eshazen/blinky-pov/AVR4/prog/prog_large.png

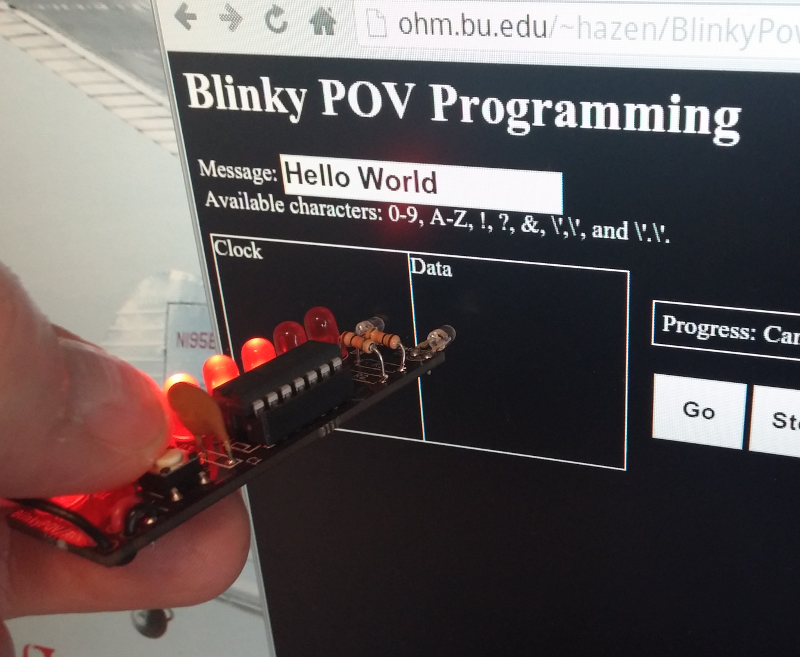
AVR4/prog/prog_large.png
