eshazen/blinky-pov/BlinkyColorPOV/pix/2015-11-30 16.28.32.jpg

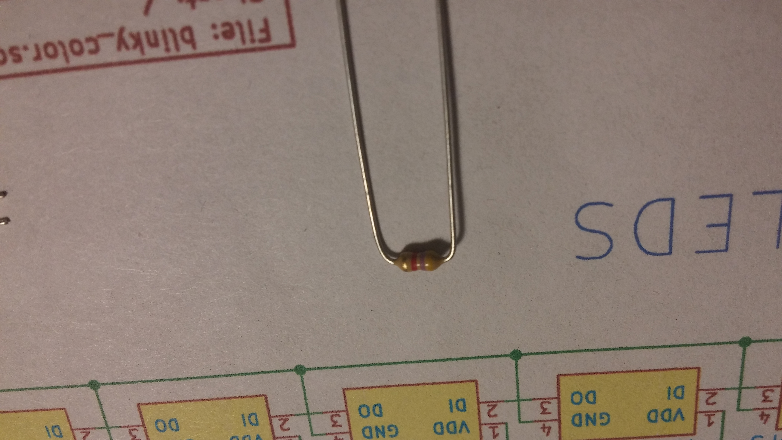
BlinkyColorPOV/pix/2015-11-30 16.28.32.jpg
