eshazen/blinky-pov/BlinkyColorPOV/pix/2015-11-30 16.30.00.jpg

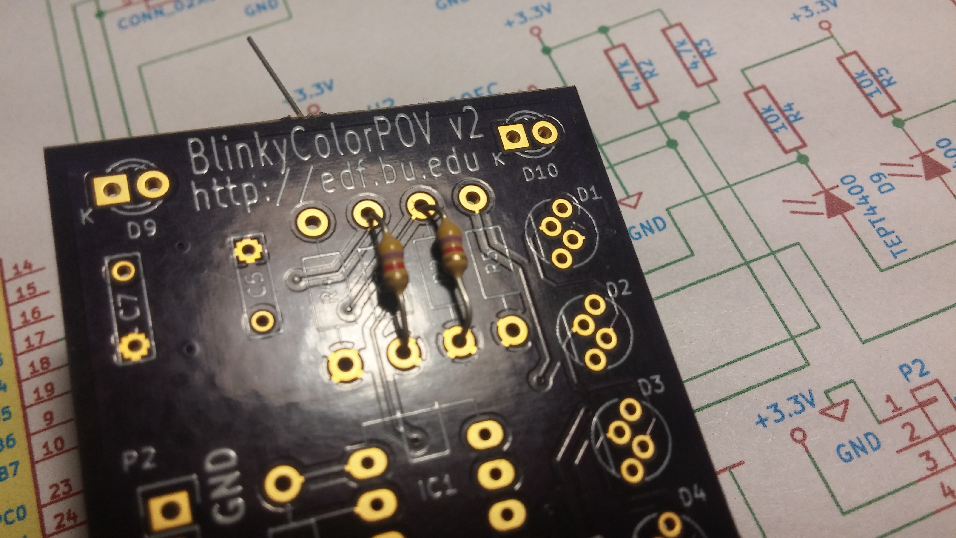
BlinkyColorPOV/pix/2015-11-30 16.30.00.jpg
