eshazen/blinky-pov/BlinkyColorPOV/pix/2015-11-30 16.31.33.jpg

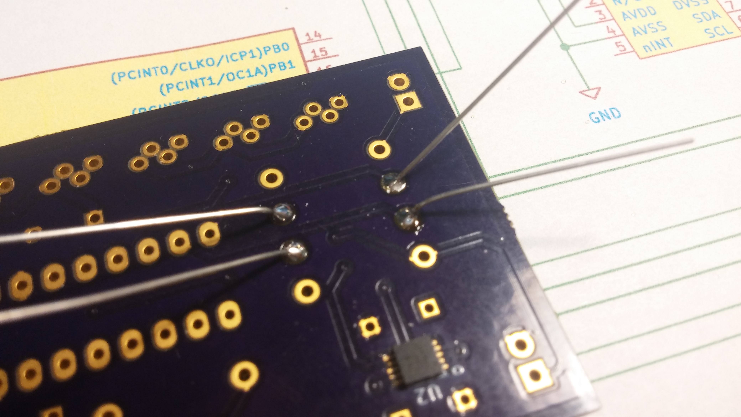
BlinkyColorPOV/pix/2015-11-30 16.31.33.jpg
