eshazen/blinky-pov/BlinkyColorPOV/pix/2015-11-30 16.32.19.jpg

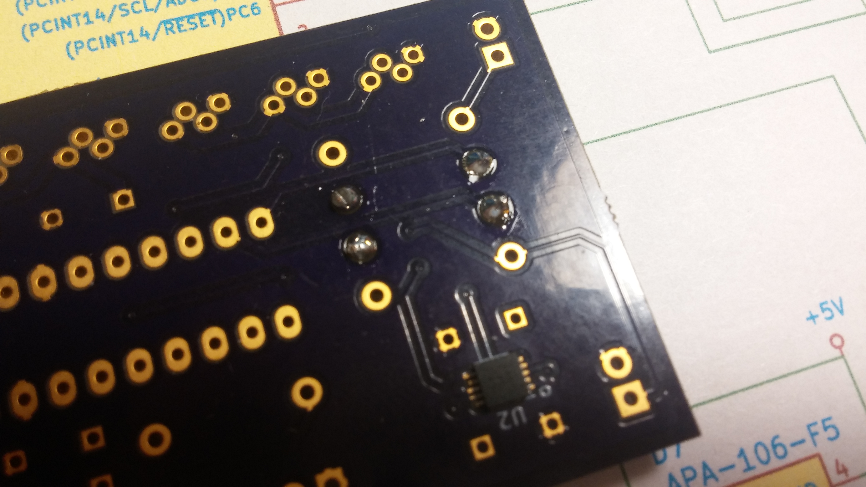
BlinkyColorPOV/pix/2015-11-30 16.32.19.jpg
