eshazen/blinky-pov/BlinkyColorPOV/pix/2015-11-30 16.37.39.jpg

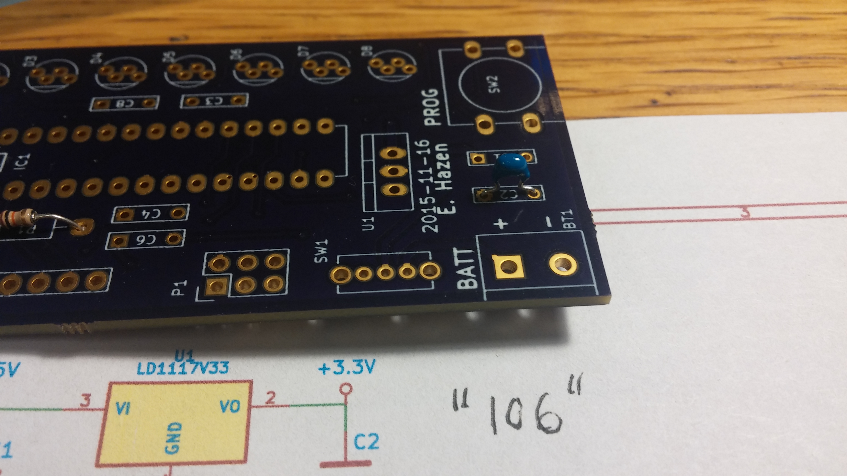
BlinkyColorPOV/pix/2015-11-30 16.37.39.jpg
