eshazen/blinky-pov/BlinkyColorPOV/pix/2015-11-30 16.41.47.jpg

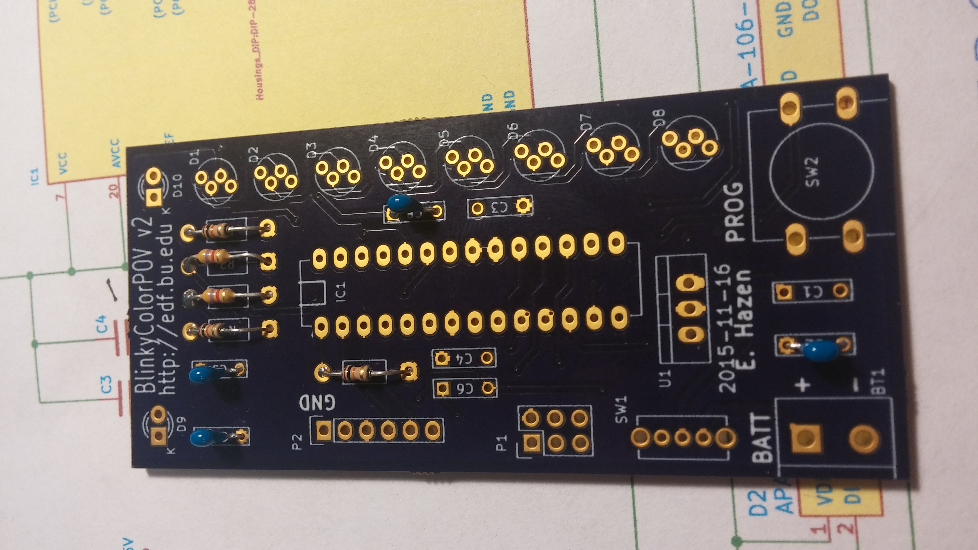
BlinkyColorPOV/pix/2015-11-30 16.41.47.jpg
