eshazen/blinky-pov/BlinkyColorPOV/pix/2015-11-30 16.43.27.jpg

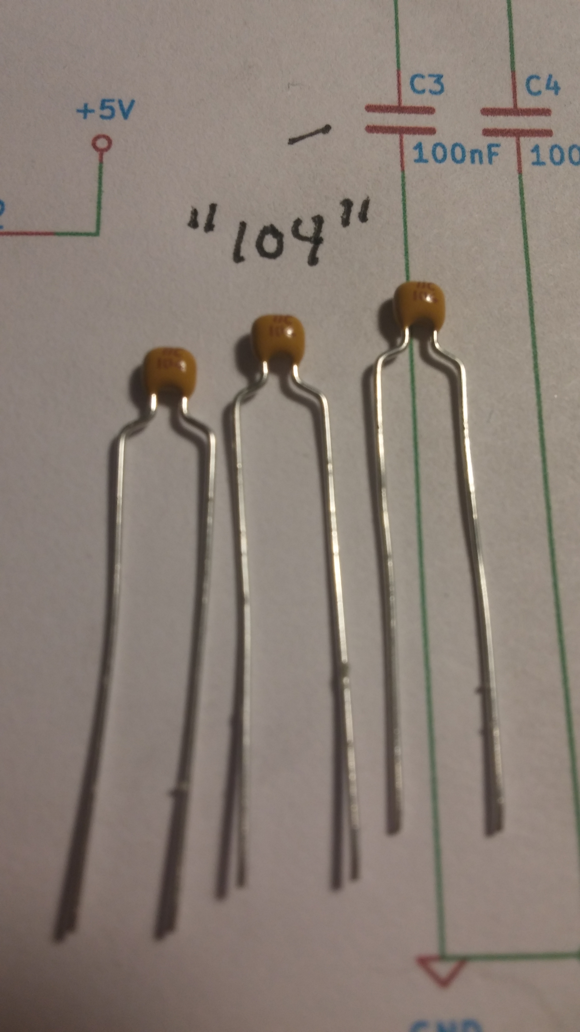
BlinkyColorPOV/pix/2015-11-30 16.43.27.jpg
