eshazen/blinky-pov/BlinkyColorPOV/pix/2015-11-30 16.45.30.jpg

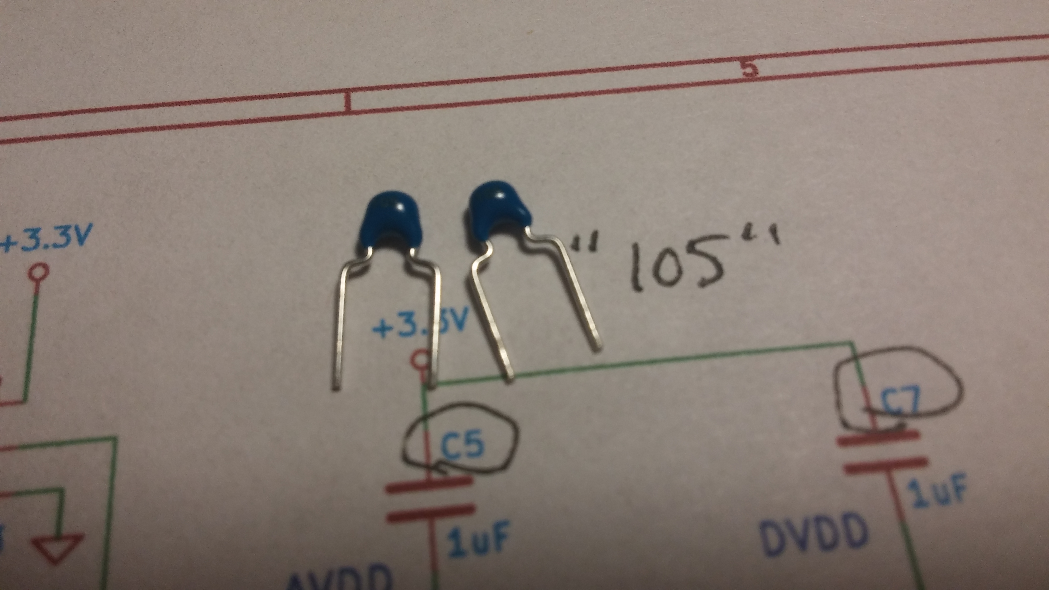
BlinkyColorPOV/pix/2015-11-30 16.45.30.jpg
