eshazen/blinky-pov/BlinkyColorPOV/pix/2015-11-30 16.46.09.jpg

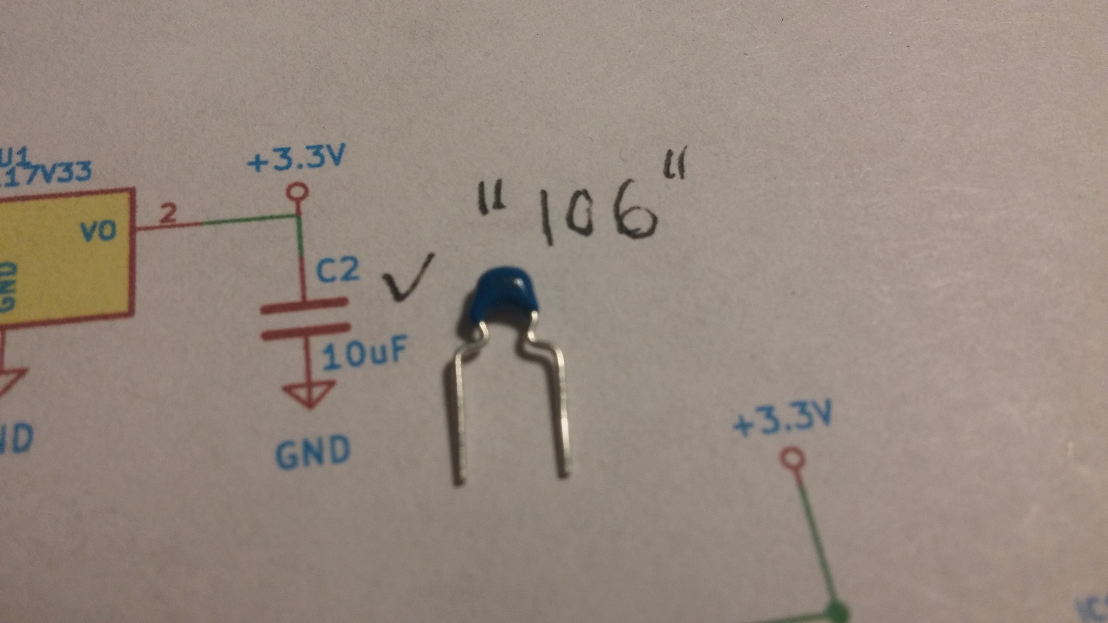
BlinkyColorPOV/pix/2015-11-30 16.46.09.jpg
