eshazen/blinky-pov/BlinkyColorPOV/pix/2015-11-30 16.52.55.jpg

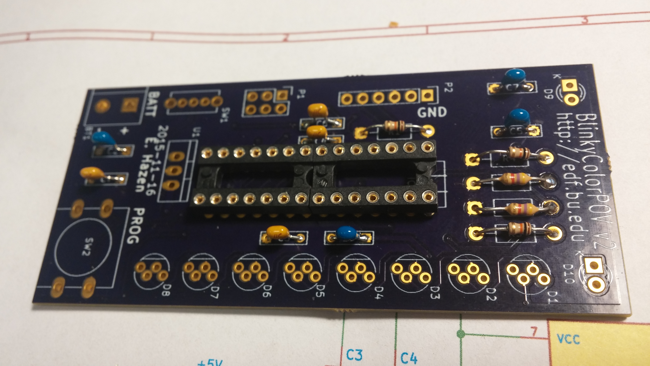
BlinkyColorPOV/pix/2015-11-30 16.52.55.jpg
