eshazen/blinky-pov/BlinkyColorPOV/pix/2015-11-30 16.53.03.jpg

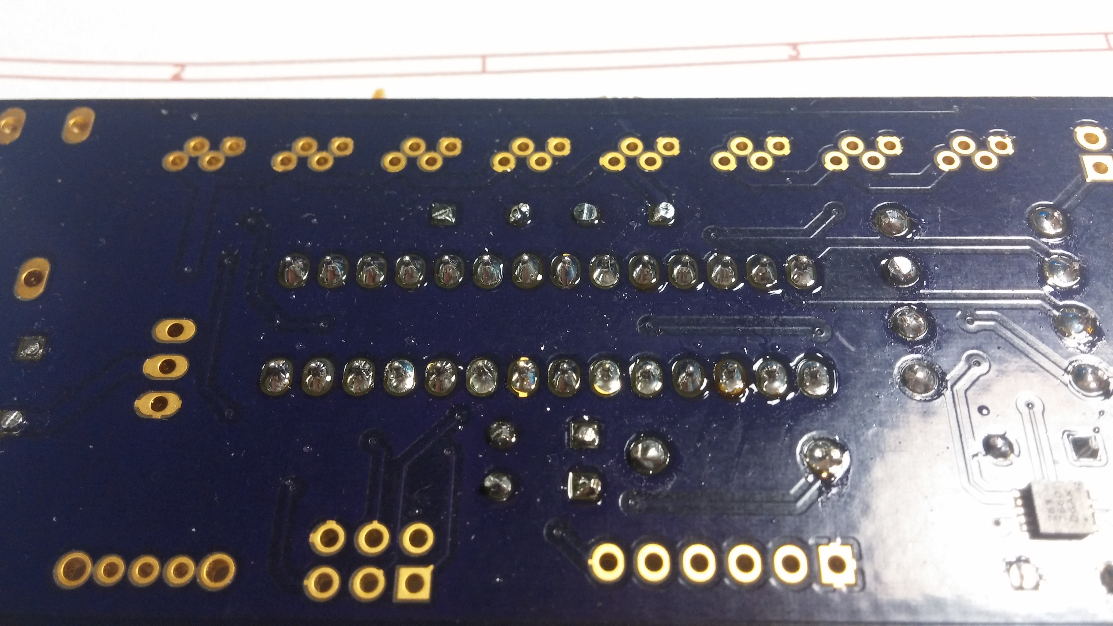
BlinkyColorPOV/pix/2015-11-30 16.53.03.jpg
