eshazen/blinky-pov/BlinkyColorPOV/pix/2015-11-30 16.54.51.jpg

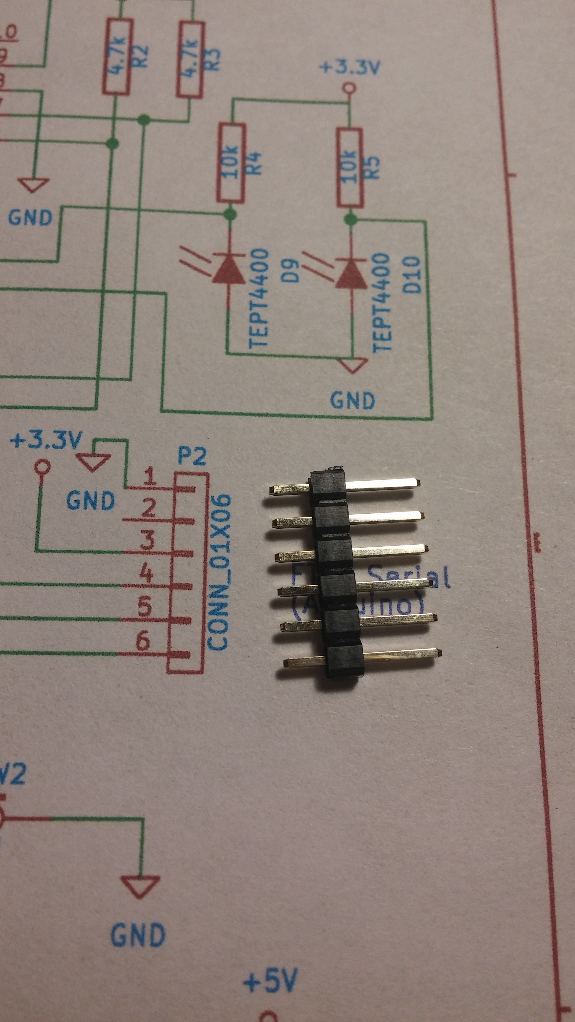
BlinkyColorPOV/pix/2015-11-30 16.54.51.jpg
