eshazen/blinky-pov/BlinkyColorPOV/pix/2015-11-30 16.56.59.jpg

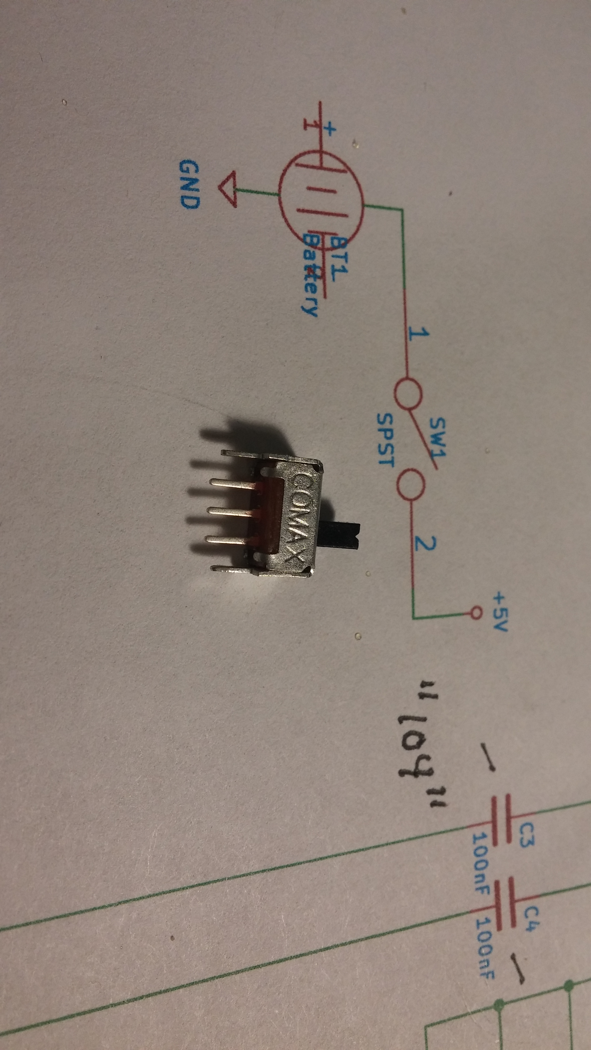
BlinkyColorPOV/pix/2015-11-30 16.56.59.jpg
