eshazen/blinky-pov/BlinkyColorPOV/pix/2015-11-30 16.58.29.jpg

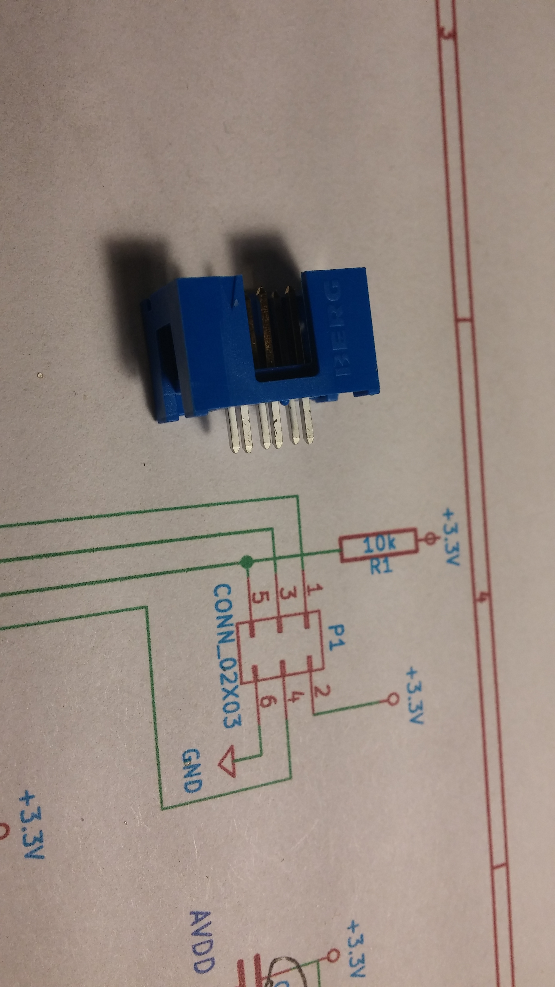
BlinkyColorPOV/pix/2015-11-30 16.58.29.jpg
