eshazen/blinky-pov/BlinkyColorPOV/pix/2015-11-30 16.59.57.jpg

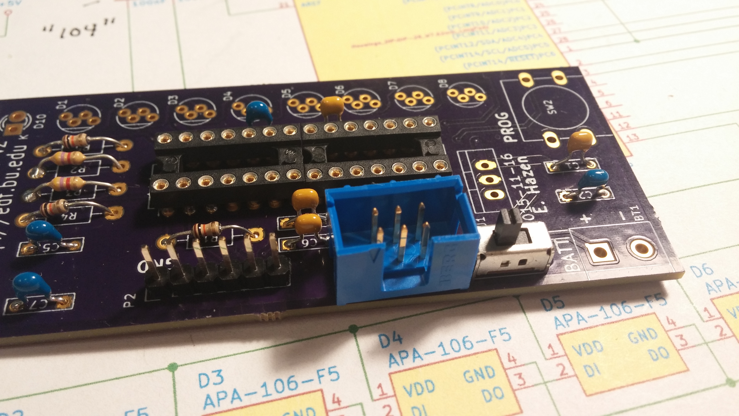
BlinkyColorPOV/pix/2015-11-30 16.59.57.jpg
