eshazen/blinky-pov/BlinkyColorPOV/pix/2015-11-30 17.00.21.jpg

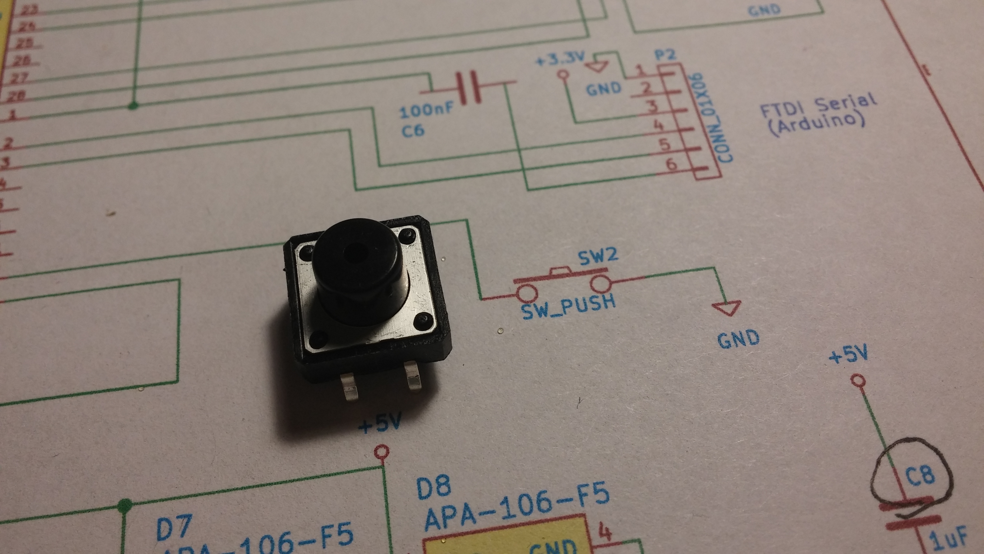
BlinkyColorPOV/pix/2015-11-30 17.00.21.jpg
