eshazen/blinky-pov/BlinkyColorPOV/pix/2015-11-30 17.01.27.jpg

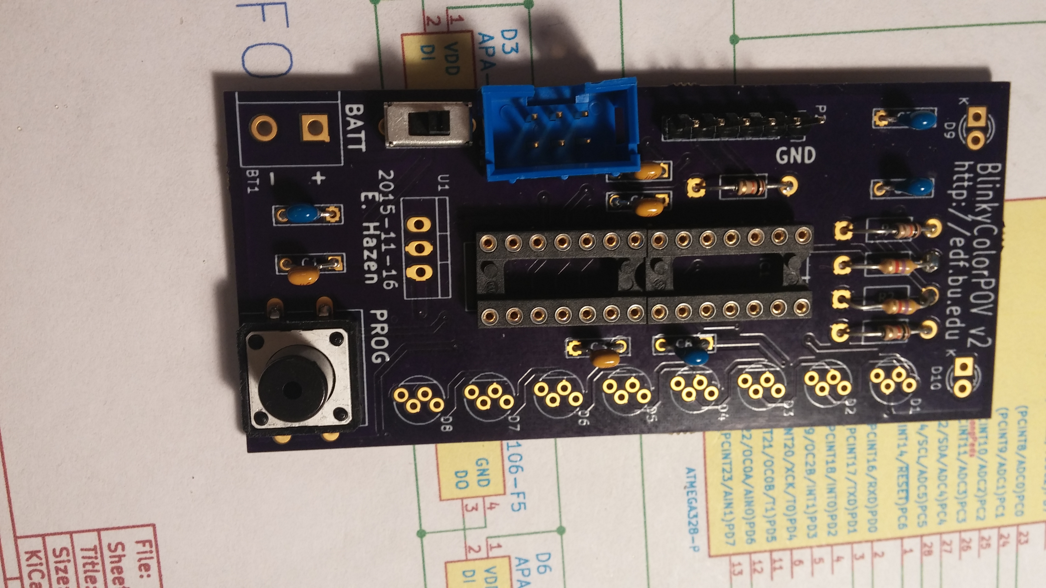
BlinkyColorPOV/pix/2015-11-30 17.01.27.jpg
