eshazen/blinky-pov/BlinkyColorPOV/pix/2015-11-30 17.02.28.jpg

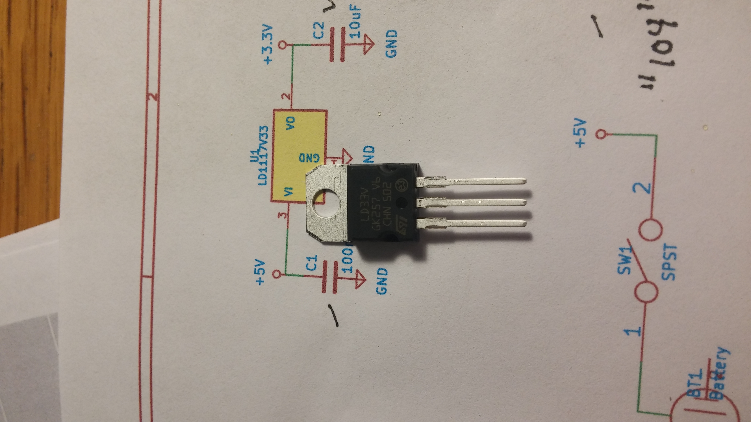
BlinkyColorPOV/pix/2015-11-30 17.02.28.jpg
