eshazen/blinky-pov/BlinkyColorPOV/pix/2015-11-30 17.03.59.jpg

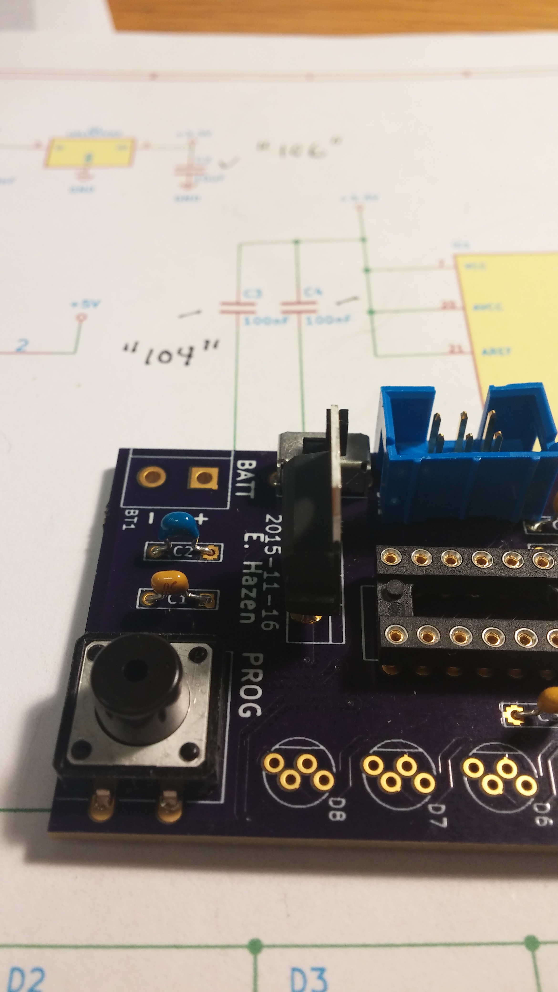
BlinkyColorPOV/pix/2015-11-30 17.03.59.jpg
