eshazen/blinky-pov/BlinkyColorPOV/pix/2015-11-30 17.05.24.jpg

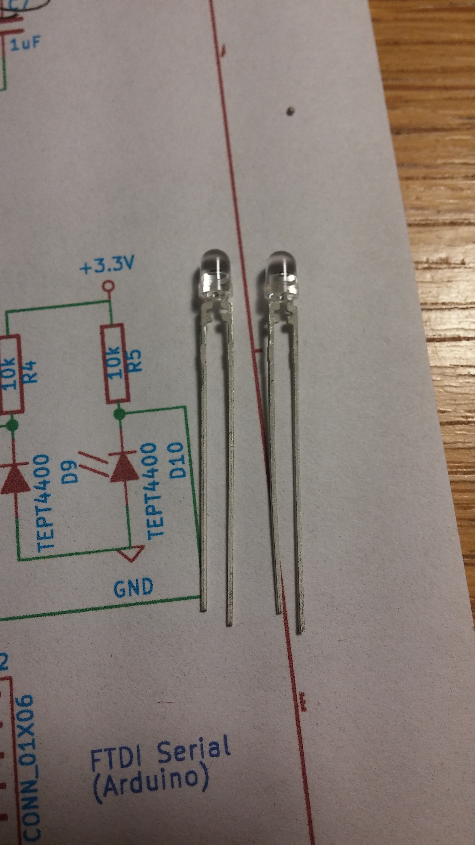
BlinkyColorPOV/pix/2015-11-30 17.05.24.jpg
