eshazen/blinky-pov/BlinkyColorPOV/pix/2015-11-30 17.06.36.jpg

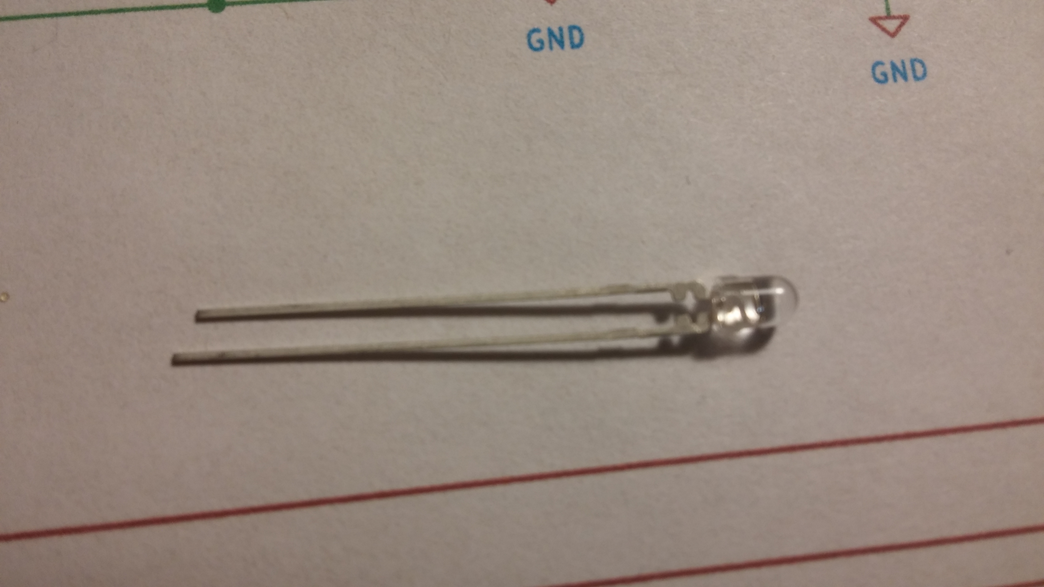
BlinkyColorPOV/pix/2015-11-30 17.06.36.jpg
