eshazen/blinky-pov/BlinkyColorPOV/pix/2015-11-30 17.07.34.jpg

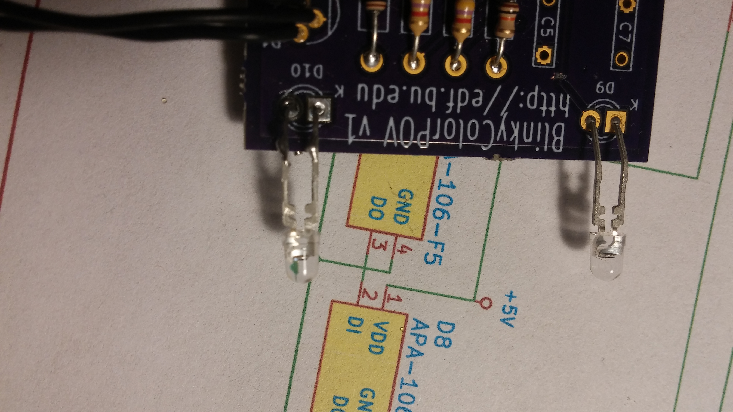
BlinkyColorPOV/pix/2015-11-30 17.07.34.jpg
