eshazen/blinky-pov/BlinkyColorPOV/pix/2015-11-30 17.08.37.jpg

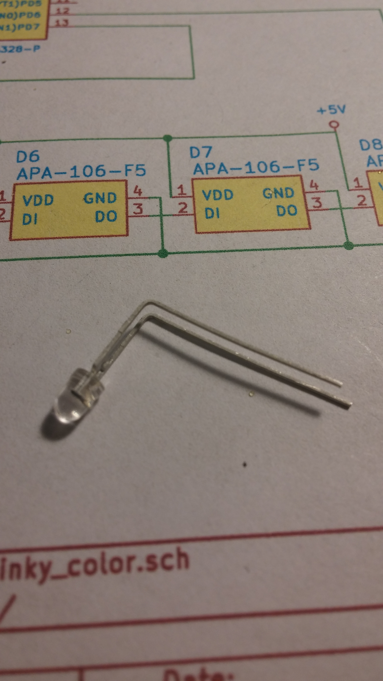
BlinkyColorPOV/pix/2015-11-30 17.08.37.jpg
