eshazen/blinky-pov/BlinkyColorPOV/pix/2015-11-30 17.10.58.jpg

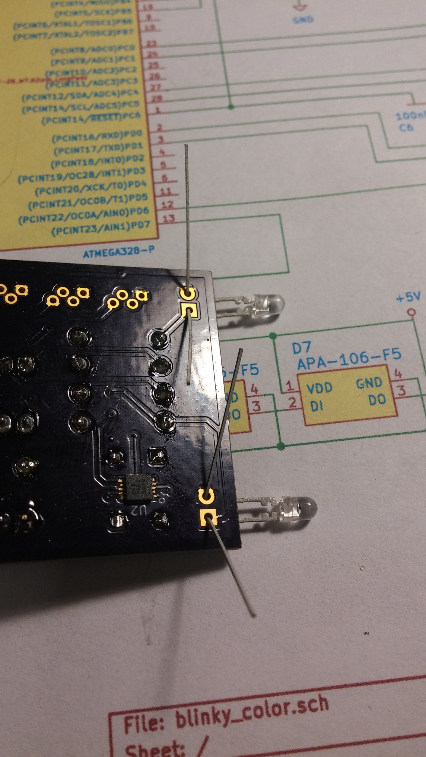
BlinkyColorPOV/pix/2015-11-30 17.10.58.jpg
