eshazen/blinky-pov/BlinkyColorPOV/pix/2015-11-30 17.13.22.jpg

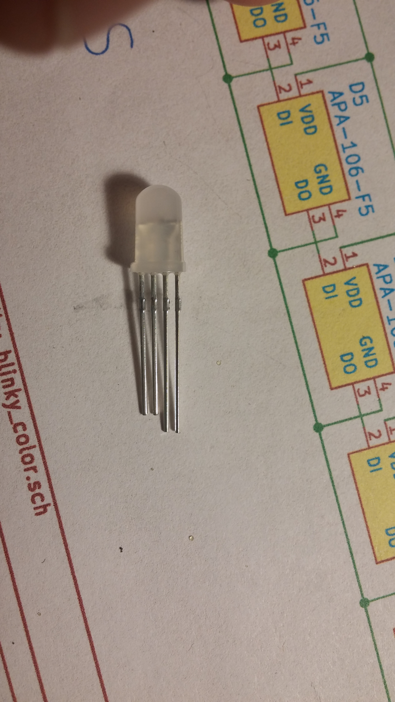
BlinkyColorPOV/pix/2015-11-30 17.13.22.jpg
