eshazen/blinky-pov/BlinkyColorPOV/pix/2015-11-30 17.14.33.jpg

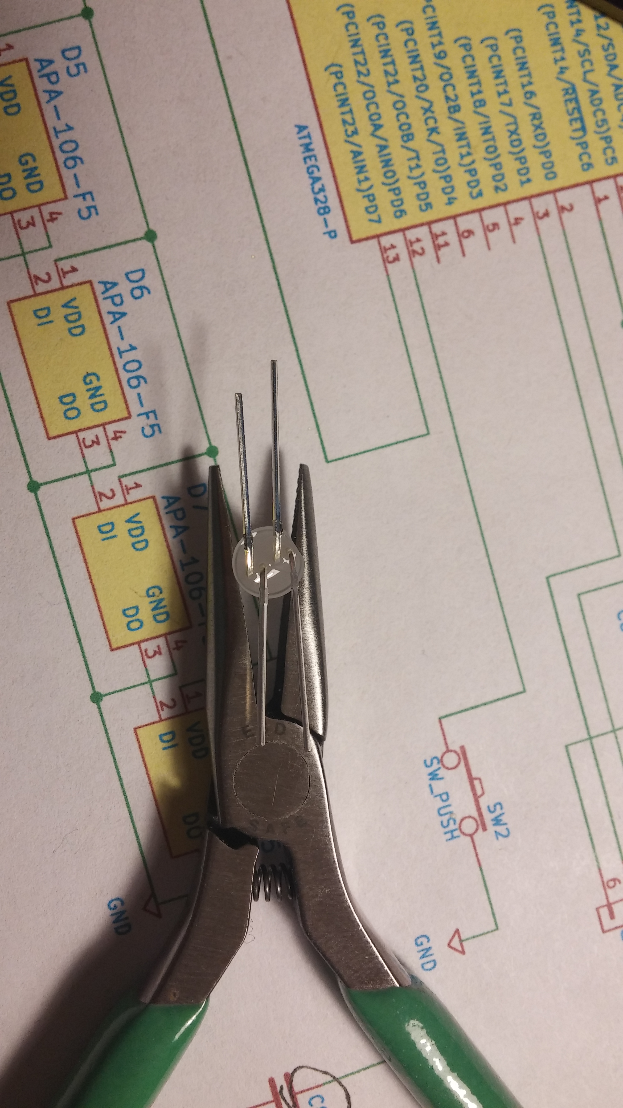
BlinkyColorPOV/pix/2015-11-30 17.14.33.jpg
