eshazen/blinky-pov/BlinkyColorPOV/pix/2015-11-30 17.16.10.jpg

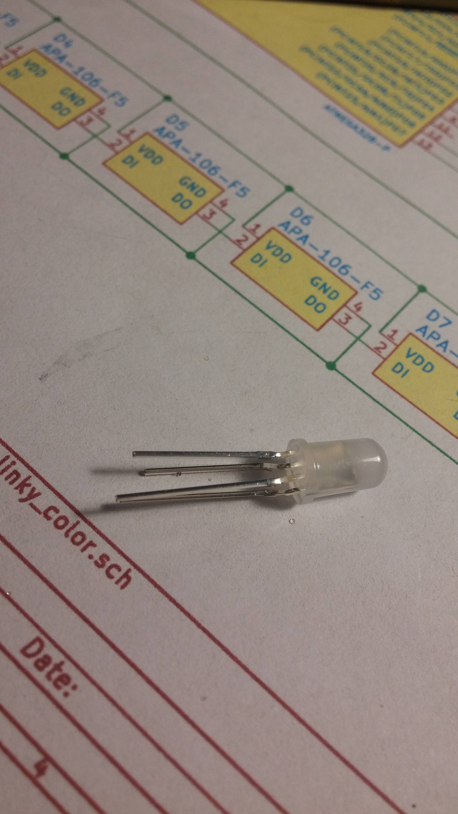
BlinkyColorPOV/pix/2015-11-30 17.16.10.jpg
