eshazen/blinky-pov/BlinkyColorPOV/pix/2015-11-30 17.17.15.jpg

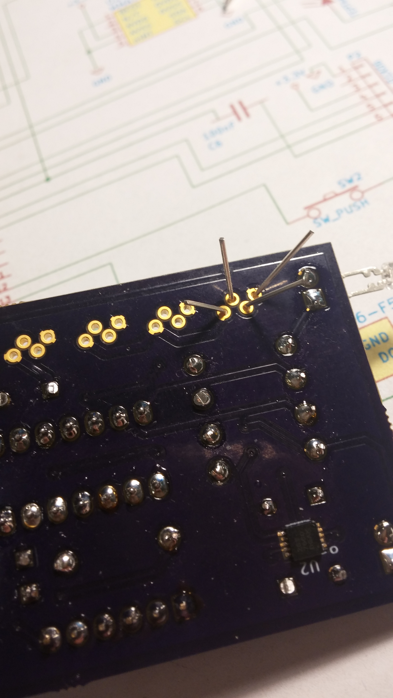
BlinkyColorPOV/pix/2015-11-30 17.17.15.jpg
