eshazen/blinky-pov/BlinkyColorPOV/pix/2015-11-30 17.18.42.jpg

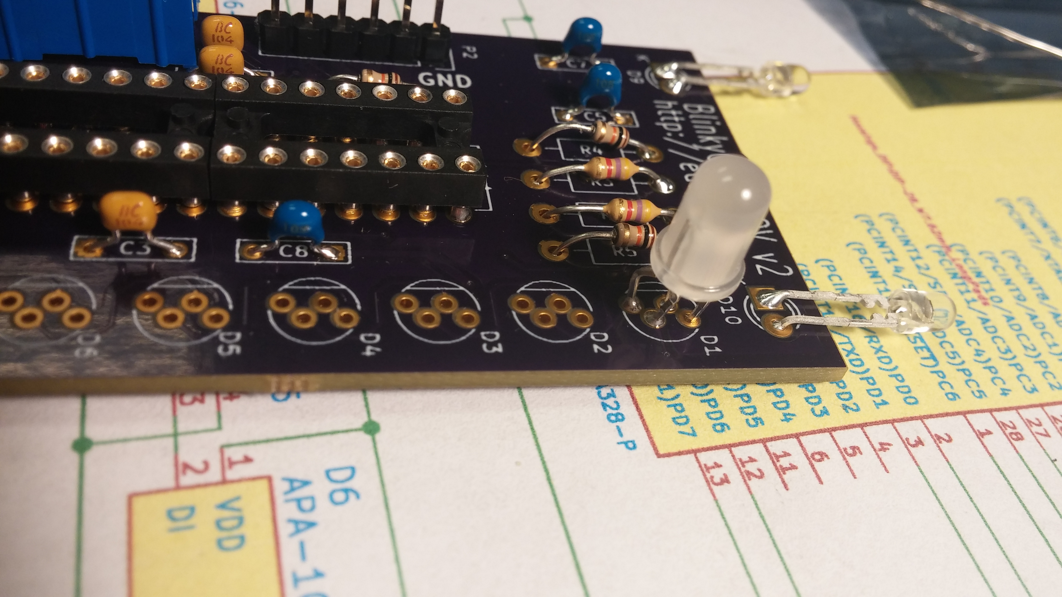
BlinkyColorPOV/pix/2015-11-30 17.18.42.jpg
