eshazen/blinky-pov/BlinkyColorPOV/pix/2015-11-30 17.19.03.jpg

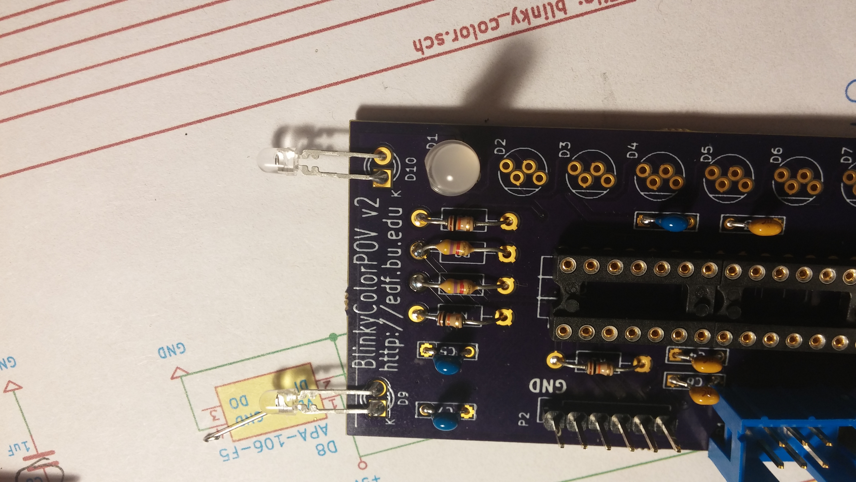
BlinkyColorPOV/pix/2015-11-30 17.19.03.jpg
