eshazen/blinky-pov/BlinkyColorPOV/Firmware/Test2/main.c

//Blinky.c

#include <avr/io.h>
#include <util/delay.h>

// #define PIXELS 1  // Number of pixels in the string

#define PIXEL_PORT  PORTD  // Port of the pin the pixels are connected to
#define PIXEL_DDR   DDRD   // Port of the pin the pixels are connected to
#define PIXEL_BIT   7      // Bit of the pin the pixels are connected to


#define T1H  900    // Width of a 1 bit in ns
#define T1L  600    // Width of a 1 bit in ns

#define T0H  400    // Width of a 0 bit in ns
#define T0L  900    // Width of a 0 bit in ns

#define RES 6000    // Width of the low gap between bits to cause a frame to latch

#define NS_PER_SEC (1000000000L)          // Note that this has to be SIGNED since we want to be
                                          // able to check for negative values of derivatives
#define CYCLES_PER_SEC (F_CPU)
#define NS_PER_CYCLE ( NS_PER_SEC / CYCLES_PER_SEC )
#define NS_TO_CYCLES(n) ( (n) / NS_PER_CYCLE )

#define bitRead(w,b) (((w)>>(b))&1)

// Actually send a bit to the string. We must to drop to asm to enusre that the complier does
// not reorder things and make it so the delay happens in the wrong place.

#define bool uint8_t

void sendBit( bool bitVal ) {
  
  if (  bitVal ) {				// 0 bit
      
    asm volatile (
		  "sbi %[port], %[bit] \n\t"				// Set the output bit
		  ".rept %[onCycles] \n\t"                                // Execute NOPs to delay exactly the specified number of cycles
		  "nop \n\t"
		  ".endr \n\t"
		  "cbi %[port], %[bit] \n\t"                              // Clear the output bit
		  ".rept %[offCycles] \n\t"                               // Execute NOPs to delay exactly the specified number of cycles
		  "nop \n\t"
		  ".endr \n\t"
		  ::
		   [port]		"I" (_SFR_IO_ADDR(PIXEL_PORT)),
		   [bit]		"I" (PIXEL_BIT),
		   [onCycles]	"I" (NS_TO_CYCLES(T1H) - 2),		// 1-bit width less overhead  for the actual bit setting, note that this delay could be longer and everything would still work
		   [offCycles] 	"I" (NS_TO_CYCLES(T1L) - 2)			// Minimum interbit delay. Note that we probably don't need this at all since the loop overhead will be enough, but here for correctness

		  );
                                  
  } else {					// 1 bit

    // **************************************************************************
    // This line is really the only tight goldilocks timing in the whole program!
    // **************************************************************************


    asm volatile (
		  "sbi %[port], %[bit] \n\t"				// Set the output bit
		  ".rept %[onCycles] \n\t"				// Now timing actually matters. The 0-bit must be long enough to be detected but not too long or it will be a 1-bit
		  "nop \n\t"                                              // Execute NOPs to delay exactly the specified number of cycles
		  ".endr \n\t"
		  "cbi %[port], %[bit] \n\t"                              // Clear the output bit
		  ".rept %[offCycles] \n\t"                               // Execute NOPs to delay exactly the specified number of cycles
		  "nop \n\t"
		  ".endr \n\t"
		  ::
		   [port]		"I" (_SFR_IO_ADDR(PIXEL_PORT)),
		   [bit]		"I" (PIXEL_BIT),
		   [onCycles]	"I" (NS_TO_CYCLES(T0H) - 2),
		   [offCycles]	"I" (NS_TO_CYCLES(T0L) - 2)

		  );
      
  }
    
  // Note that the inter-bit gap can be as long as you want as long as it doesn't exceed the 5us reset timeout (which is A long time)
  // Here I have been generous and not tried to squeeze the gap tight but instead erred on the side of lots of extra time.
  // This has thenice side effect of avoid glitches on very long strings becuase 

    
}  

  
void sendByte( unsigned char byte ) {

  uint8_t bit;
    
  for( bit = 0 ; bit < 8 ; bit++ ) {
      
    sendBit( bitRead( byte , 7 ) );                // Neopixel wants bit in highest-to-lowest order
    // so send highest bit (bit #7 in an 8-bit byte since they start at 0)
    byte <<= 1;                                    // and then shift left so bit 6 moves into 7, 5 moves into 6, etc
      
  }           
} 

/*

  The following three functions are the public API:
  
  ledSetup() - set up the pin that is connected to the string. Call once at the begining of the program.  
  sendPixel( r g , b ) - send a single pixel to the string. Call this once for each pixel in a frame.
  show() - show the recently sent pixel on the LEDs . Call once per frame. 
  
*/


// Set the specified pin up as digital out

void ledsetup() {
  PIXEL_DDR ^= (1<<PIXEL_BIT);
}

void sendPixel( unsigned char r, unsigned char g , unsigned char b )  {  
  
  sendByte(g);          // Neopixel wants colors in green then red then blue order
  sendByte(r);
  sendByte(b);
  
}


// Just wait long enough without sending any bots to cause the pixels to latch and display the last sent frame

void show() {
  _delay_us( (RES / 1000UL) + 1);				// Round up since the delay must be _at_least_ this long (too short might not work, too long not a problem)
}




int main (void)
{
  ledsetup();

  uint8_t r, g, b;

#define INTEN 20

  sendPixel( INTEN, 0, 0);
  sendPixel( 0, INTEN, 0);
  sendPixel( 0, 0, INTEN);
  sendPixel( INTEN, INTEN, 0);
  sendPixel( 0, INTEN, INTEN);
  sendPixel( INTEN, 0, INTEN);
  sendPixel( INTEN, INTEN, INTEN);
  sendPixel( INTEN/2, INTEN/4, 0);
  show();    

  while( 1)
    ;

}
