eshazen/blinky-pov/BlinkyColorPOV/DebugSoftware/sio_test.c

#include <stdio.h>

#include "sio_cmd.h"

main()
{
  char buff[255];
  char *s;
  int fd;
  
  if( (fd = sio_open("/dev/ttyS0")) < 0) {
    printf("Error opening serial port\n");
    exit( 1);
  }

  while( 1) {
    printf("cmd>");
    fgets( buff, 255, stdin);

    if( toupper( *buff) == 'Q')
      break;

    printf("Sending cmd: %s\n", buff);
    s = sio_cmd( fd, buff);
    if( s == NULL)
      printf("sio_cmd() error\n");
    else {
      printf("Got %d chars\n", strlen( s));
      dump_string( s);
    }
  }

  close( fd);
  
}
