eshazen/blinky-pov/BlinkyColorPOV/Firmware/ColorText/uart.h

#include <avr/io.h>

#define USART_BAUDRATE 9600
#define UBRR_VALUE (((F_CPU / (USART_BAUDRATE * 16UL))) - 1)

void USART0Init(void);
int USART0SendByte(char u8Data, FILE *stream);
uint8_t USART0ReceiveByte();
void USART0GetString( char *buffer, int max);
